flypie/Ace-2019/KiCad/ACE3NOKB/Gerber/May 5/ACE3NOKB-B_Mask.pdf

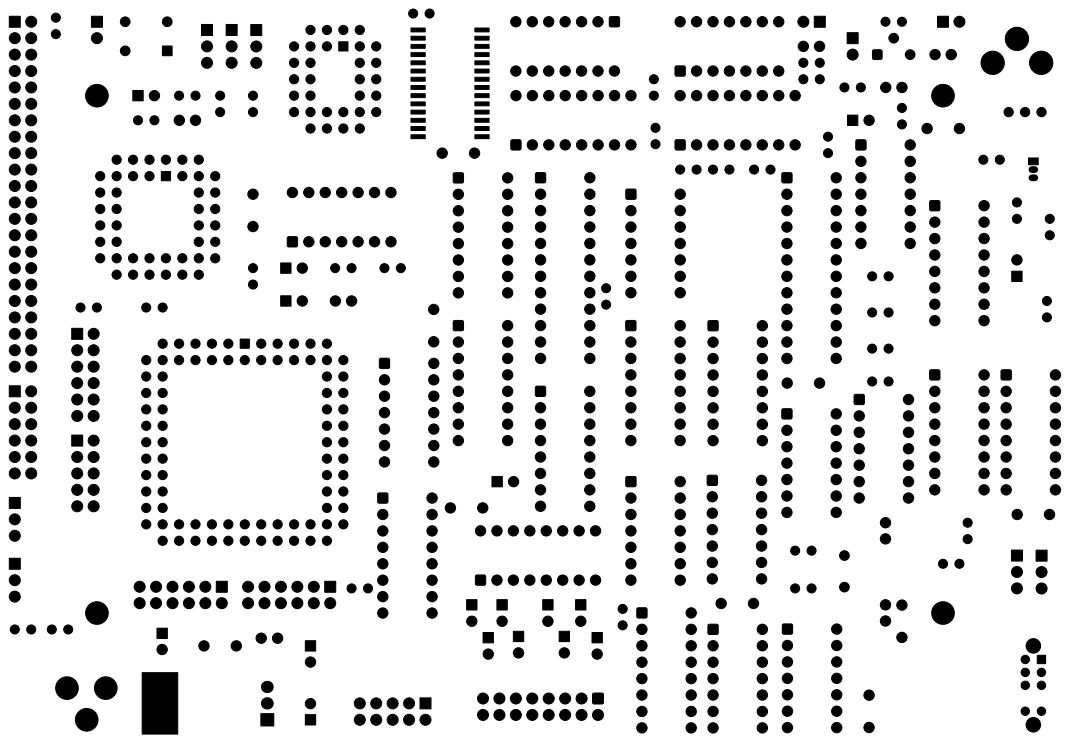
[picture p18: page 1]
