flypie/Ace-2019/KiCad/ACE3NOKB/Gerber/May 5/ACE3NOKB-B_Paste.pdf

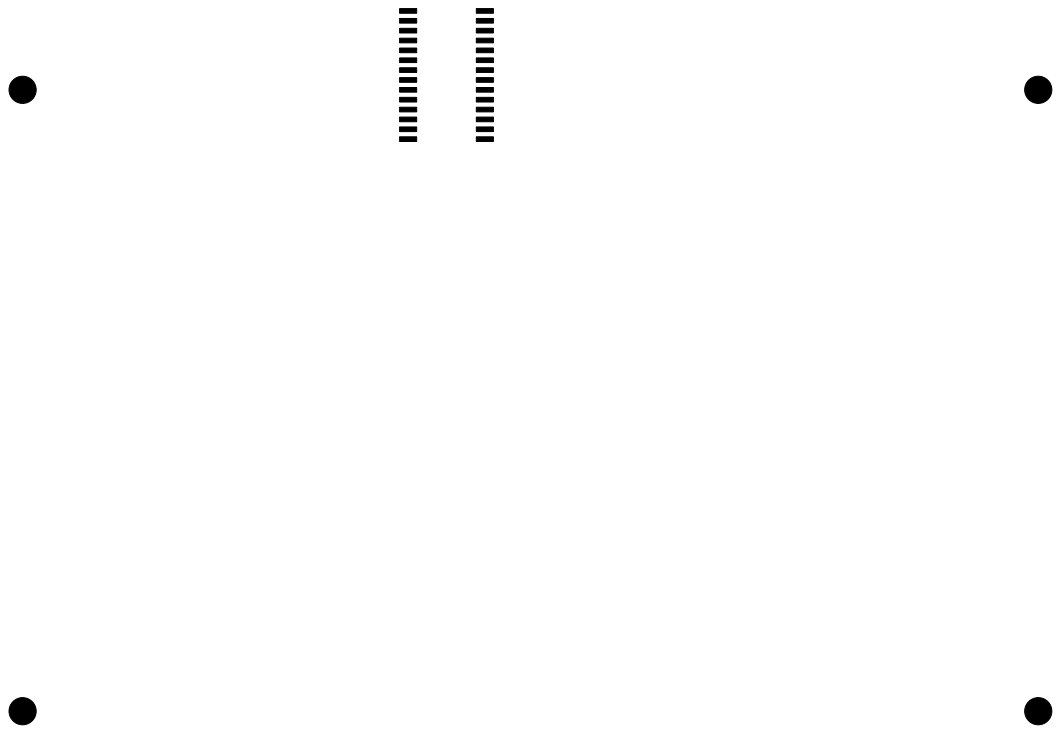
[picture p19: page 1]
