flypie/Ace-2019/KiCad/ACE3NOKB/Gerber/May 5/ACE3NOKB-B_Silkscreen.pdf

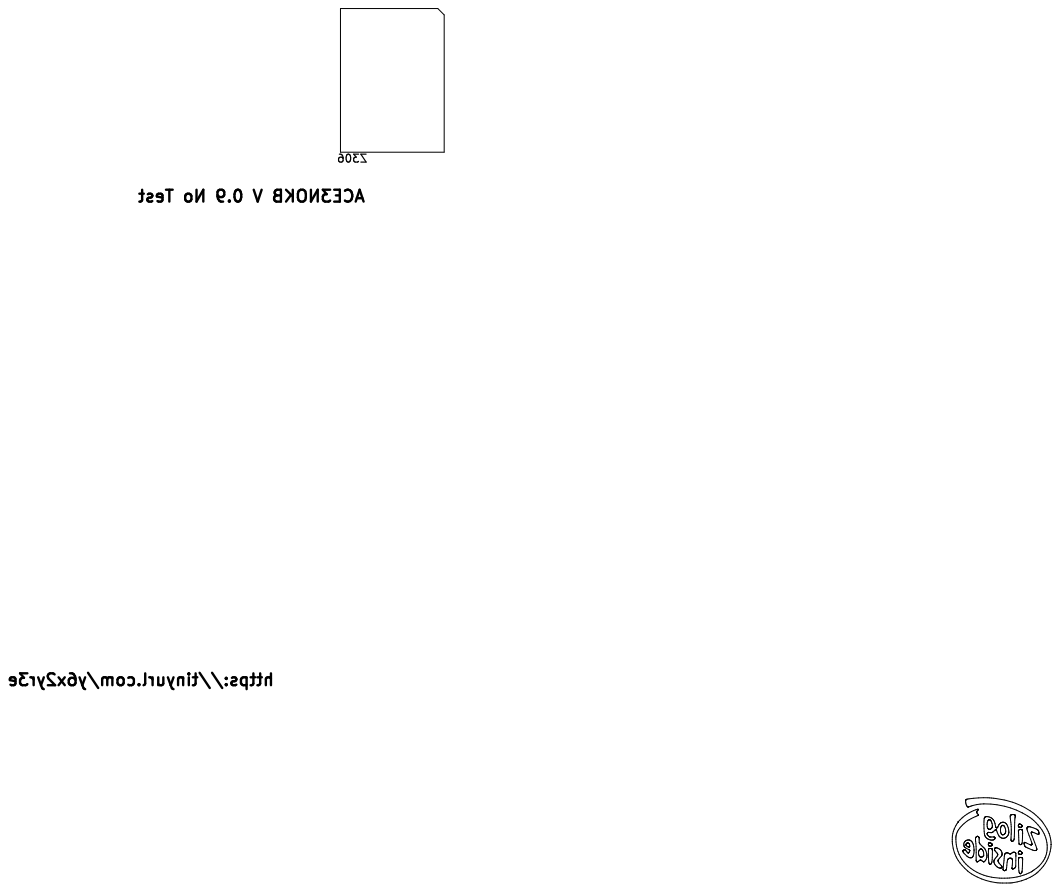
[picture p20: page 1]
