flypie/Ace-2019/KiCad/ACE3NOKB/Gerber/May 5/ACE3NOKB-Bottom.pdf

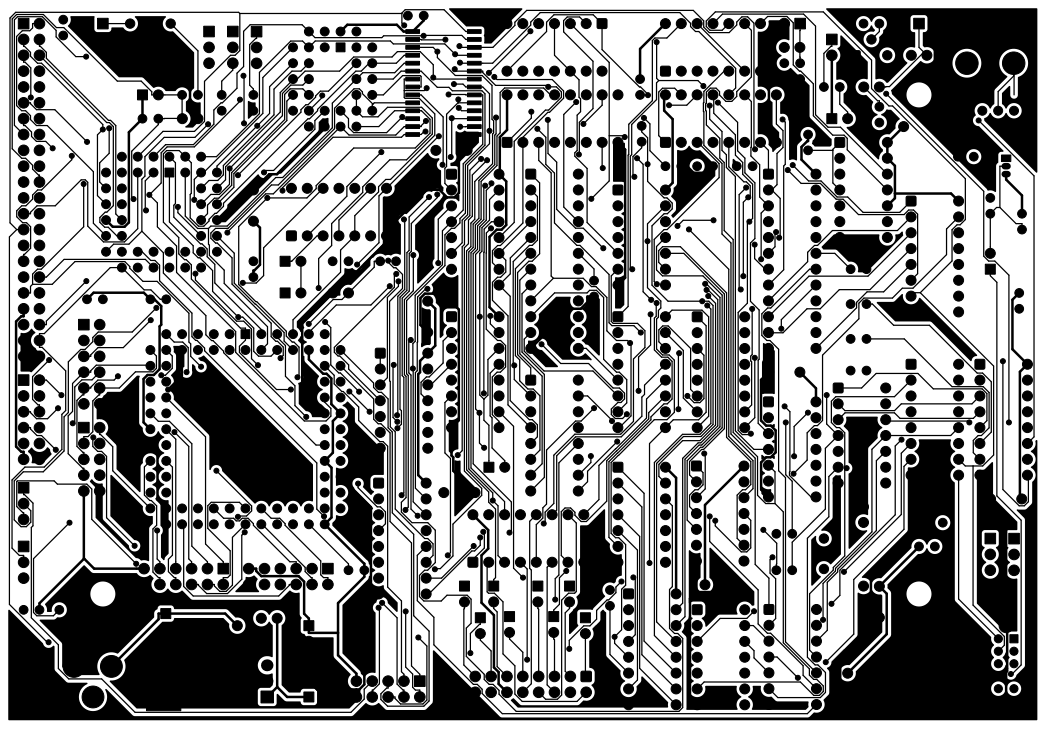
[picture p21: page 1]
