flypie/Ace-2019/KiCad/ACE3NOKB/Gerber/May 5/ACE3NOKB-F_Mask.pdf

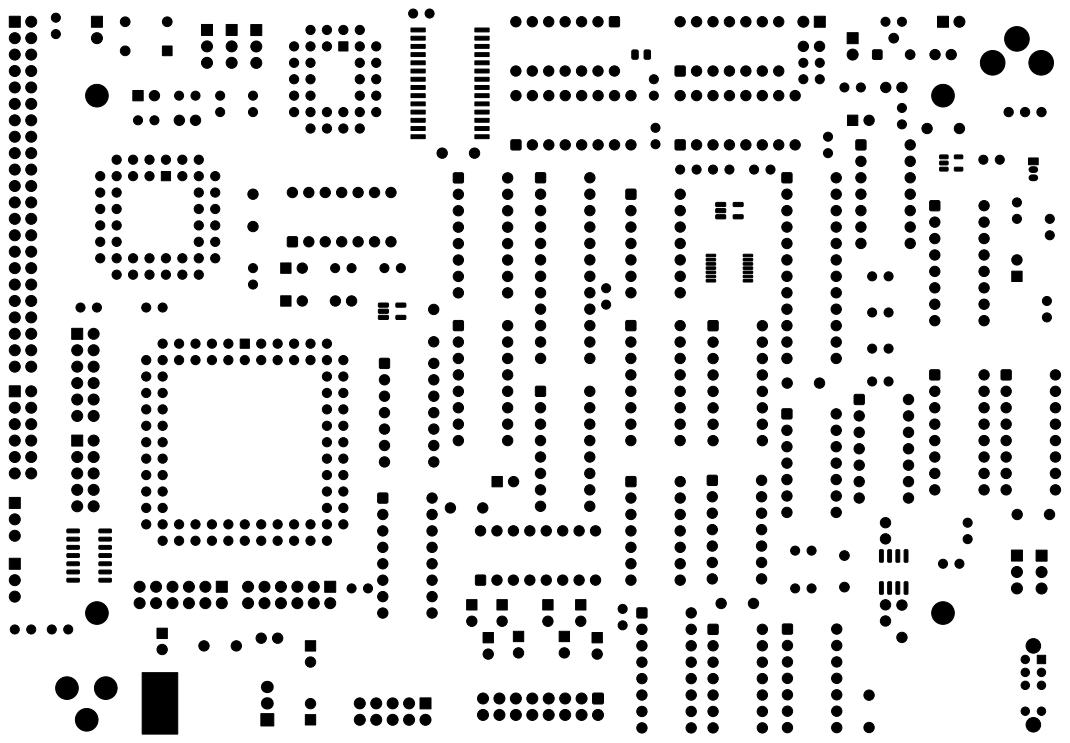
[picture p22: page 1]
