flypie/Ace-2019/KiCad/ACE3NOKB/Gerber/May 5/ACE3NOKB-F_Paste.pdf

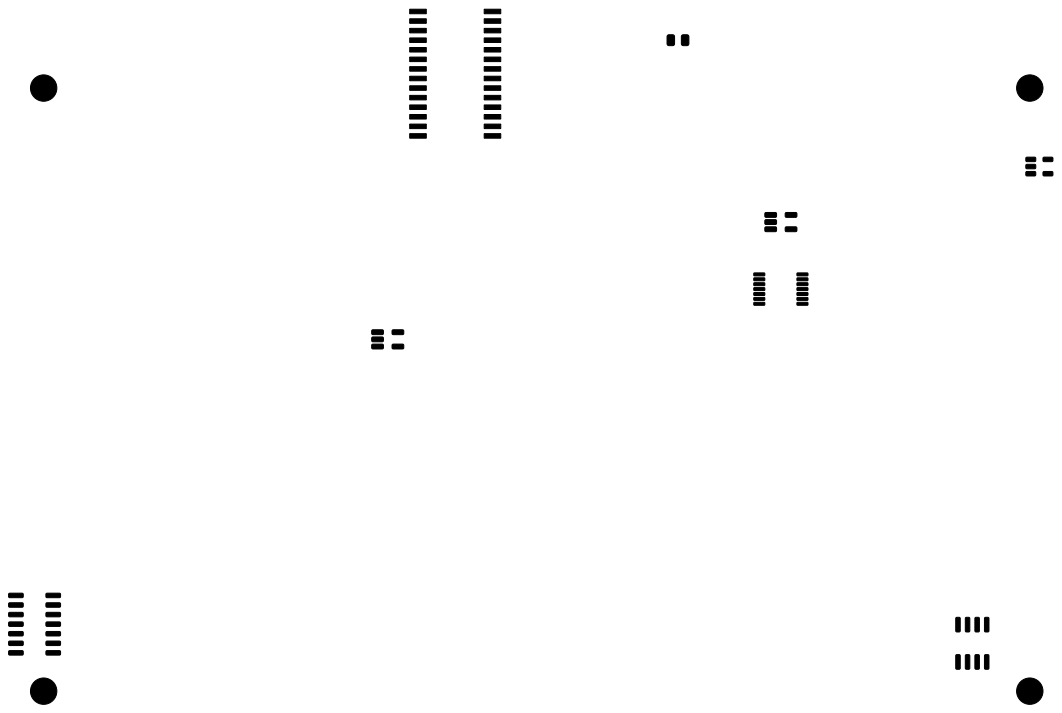
[picture p23: page 1]
