flypie/Ace-2019/KiCad/ACE3NOKB/Gerber/May 5/ACE3NOKB-F_Silkscreen.pdf

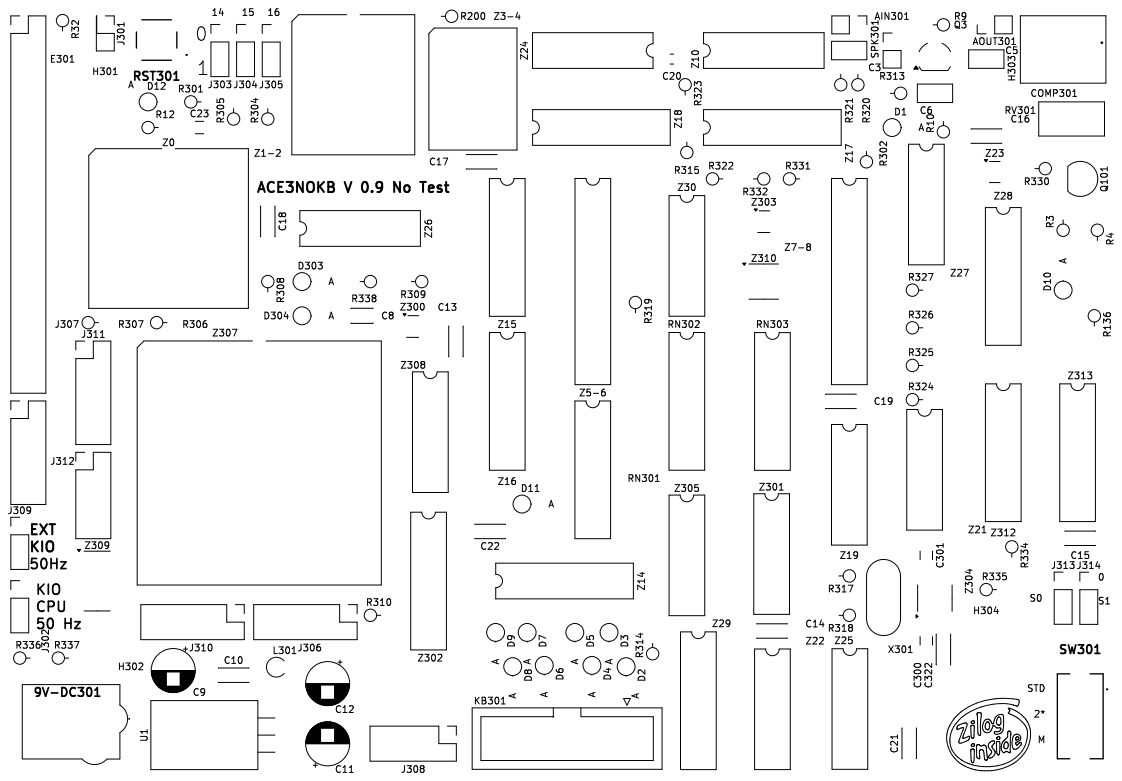
[picture p24: page 1]
