flypie/Ace-2019/KiCad/ACE3NOKB/Gerber/May 5/ACE3NOKB-Top.pdf

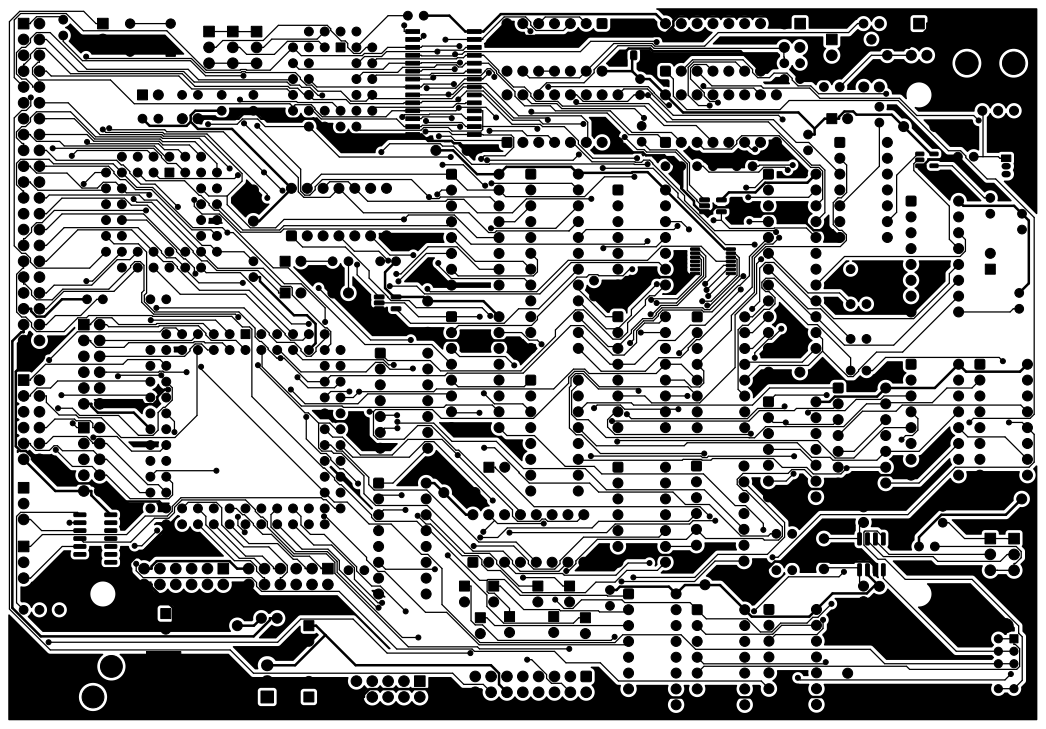
[picture p25: page 1]
